jit89/Home-Automation/Hardware/rev_1.0/eagle_schematic.sch

## EAGLE design Hardware/rev_1.0/eagle_schematic.sch (2018-12-20)

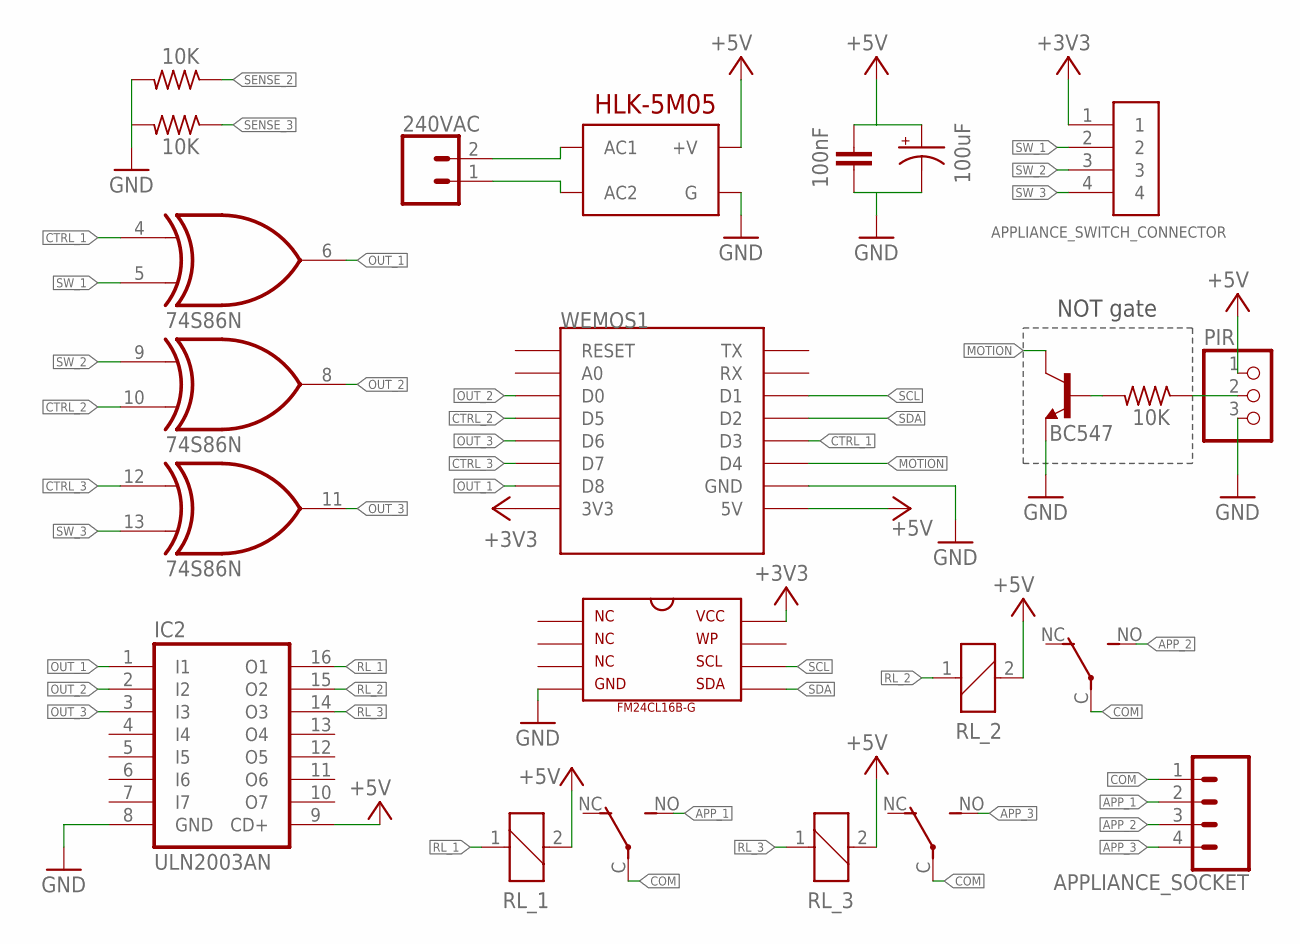
[picture p13: schematic eagle_schematic.sch]

Parts:
240VAC: CONN_025MM; SCREWTERMINAL-5MM-2
APPLIANCE_SOCKET: CONN_04SCREW_LOCK; SCREWTERMINAL-3.5MM-4_LOCK
APPLIANCE_SWITCH_CONNECTOR: 1X4-BIG; 1X04-BIG
C1: 100nF; C5B2.5
C2: 100uF; B45181B
IC1: 74S86N; DIL14
IC2: ULN2003AN; DIL16
PIR: PINHD-1X3CB; 1X03-CLEANBIG
R1, R2, R3: 10K; 0204/7
RL_1, RL_2, RL_3: CQ1-12V; CQ1
T1: BC547; TO92
U$1: HLK-5M05
U$3: FM24CL16B-G
WEMOS1: WEMOS-D1-MINI

Connections:
+3V3: APPLIANCE_SWITCH_CONNECTOR.1, U$3.8, WEMOS1.3V3
+5V: C1.1, C2.+, IC2.9 (CD+), PIR.1, RL_1.2, RL_2.2, RL_3.2, U$1.+V, WEMOS1.5V
APP_1: APPLIANCE_SOCKET.2, RL_1.NO (S)
APP_2: APPLIANCE_SOCKET.3, RL_2.NO (S)
APP_3: APPLIANCE_SOCKET.4, RL_3.NO (S)
COM: APPLIANCE_SOCKET.1, RL_1.C, RL_2.C, RL_3.C
CTRL_1: IC1.4 (I0), WEMOS1.D3
CTRL_2: IC1.10 (I1), WEMOS1.D5
CTRL_3: IC1.12 (I0), WEMOS1.D7
GND: C1.2, C2.-, IC2.8 (GND), PIR.3, R2.2, R3.2, T1.1 (E), U$1.G, U$3.4, WEMOS1.GND
MOTION: T1.3 (C), WEMOS1.D4
unnamed: R1.2, T1.2 (B)
unnamed: PIR.2, R1.1
unnamed: 240VAC.2, U$1.AC1
unnamed: 240VAC.1, U$1.AC2
OUT_1: IC1.6 (O), IC2.1 (I1), WEMOS1.D8
OUT_2: IC1.8 (O), IC2.2 (I2), WEMOS1.D0
OUT_3: IC1.11 (O), IC2.3 (I3), WEMOS1.D6
RL_1: IC2.16 (O1), RL_1.1
RL_2: IC2.15 (O2), RL_2.1
RL_3: IC2.14 (O3), RL_3.1
SCL: U$3.6, WEMOS1.D1
SDA: U$3.5, WEMOS1.D2
SENSE_2: R2.1
SENSE_3: R3.1
SW_1: APPLIANCE_SWITCH_CONNECTOR.2, IC1.5 (I1)
SW_2: APPLIANCE_SWITCH_CONNECTOR.3, IC1.9 (I0)
SW_3: APPLIANCE_SWITCH_CONNECTOR.4, IC1.13 (I1)

Notes on the sheet:
NOT gate
