jit89/Home-Automation/Smartphone_Application/app/src/main/java/com/example/rak3sh/smarthome_app/MainActivity.java

package com.example.rak3sh.smarthome_app;

import android.content.Context;
import android.content.Intent;
import android.net.ConnectivityManager;
import android.net.NetworkInfo;
import android.os.AsyncTask;
import android.os.Bundle;
import android.support.v7.app.AppCompatActivity;
import android.util.Log;
import android.view.View;
import android.widget.ImageButton;
import android.widget.SeekBar;
import android.widget.Spinner;
import android.widget.TextView;
import android.widget.Toast;

import org.json.JSONObject;

import java.io.BufferedReader;
import java.io.BufferedWriter;
import java.io.InputStreamReader;
import java.io.OutputStream;
import java.io.OutputStreamWriter;
import java.net.HttpURLConnection;
import java.net.URL;
import java.net.URLEncoder;
import java.util.Iterator;

import javax.net.ssl.HttpsURLConnection;

public class MainActivity extends AppCompatActivity {


    public String ur = "http://ptsv2.com/t/vbvn/post"; //<<<<<<---url here

    //// TODO: 4/16/2018 onstart status changes


    boolean imButtonStat11 = false;         //ButtonState for on off checking
    boolean imButtonStat21=false;
    boolean imButtonStat31= false;
    boolean imButtonStat41=false;
    boolean imButtonStat12 = false;         //ButtonState for on off checking
    boolean imButtonStat22=false;
    boolean imButtonStat32= false;
    boolean imButtonStat42=false;
    boolean imButtonStat13 = false;         //ButtonState for on off checking
    boolean imButtonStat23=false;
    boolean imButtonStat33= false;
    boolean imButtonStat43=false;
    

    boolean app11, app21, app31, app41,app12,app22,app32,app42,app13,app23,app33 = false,app43;         //bools for json
    int seeka1= 0;
    int seeka2=0;
    int seeka3=0;
    int seekb1=0;
    int seekb2=0;
    int seekb3=0;
    int room=1;


    ImageButton imageButton1,imageButton2,imageButton3,imageButton4,infoButton,roomim1,roomim2,roomim3;

    TextView connectionCheckText;
    TextView appText1,appText2,appText3,appText4;
    SeekBar seekbar1,seekbar2;
     private Spinner spinner2;


    @Override
    protected void onCreate(Bundle savedInstanceState) {

        super.onCreate(savedInstanceState);
        setContentView(R.layout.activity_main);

        imageButton1 = (ImageButton) findViewById(R.id.imButton1);
        imageButton2 = (ImageButton) findViewById(R.id.imButton2);
        imageButton3 = (ImageButton) findViewById(R.id.imButton3);
        imageButton4 = (ImageButton) findViewById(R.id.imButton4);
        infoButton = (ImageButton) findViewById(R.id.infoButton);
        roomim1 = (ImageButton) findViewById(R.id.imroomButton1);
        roomim2 = (ImageButton) findViewById(R.id.imroomButton2);
        roomim3 = (ImageButton) findViewById(R.id.imroomButton3);

        appText1 = (TextView) findViewById(R.id.appText1);
        appText2 = (TextView) findViewById(R.id.appText2);
        appText3 = (TextView) findViewById(R.id.appText3);
        appText4 = (TextView) findViewById(R.id.appText4);

        //connectionCheckText = (TextView) findViewById(R.id.connectionCheckText);

        seekbar1 = (SeekBar) findViewById(R.id.seekBar1);
        seekbar2 = (SeekBar) findViewById(R.id.seekBar2);

        //spinner2=(Spinner)findViewById(R.id.spinner2);


        roomim1.performClick();

        //============================>>>>>>>>>>>info<<<<<<<<<<<<<<<==============================
        infoButton.setOnClickListener(new View.OnClickListener() {
            @Override
            public void onClick(View v) {
                Intent info = new Intent(MainActivity.this, NewActivity.class);
                startActivity(info);
            }
        });


//==============================>>>>>>>>>>>app1<<<<<<<<<<<<<<<<<<===============================
        imageButton1.setOnClickListener(new View.OnClickListener() {
            @Override
            public void onClick(View v) {
                if(room==1) {

                    if (imButtonStat11 == false) {
                        imButtonStat11 = true;
                        // Toast.makeText(getApplicationContext(),"FAN ON",Toast.LENGTH_LONG).show();
                        seekbar1.setProgress(50);
                        seeka1 = 50;
                        appText1.setText("FAN ON (50%)");
                        app11 = true;
                    } else {
                        imButtonStat11 = false;
                        //Toast.makeText(getApplicationContext(),"FAN OFF",Toast.LENGTH_LONG).show();
                        appText1.setText("FAN OFF");
                        seekbar1.setProgress(0);
                        seeka1 = 0;
                        app11 = false;
                    }
                    checkConnection();                //checking connection
                    new postReq().execute();
                }
                else if(room==2){

                    if (imButtonStat12 == false) {
                        imButtonStat12 = true;
                        // Toast.makeText(getApplicationContext(),"FAN ON",Toast.LENGTH_LONG).show();
                        seekbar1.setProgress(50);
                        seeka2 = 50;
                        appText1.setText("FAN ON (50%)");
                        app12 = true;
                    } else {
                        imButtonStat12 = false;
                        //Toast.makeText(getApplicationContext(),"FAN OFF",Toast.LENGTH_LONG).show();
                        appText1.setText("FAN OFF");
                        seekbar1.setProgress(0);
                        seeka2 = 0;
                        app12 = false;
                    }
                    checkConnection();                //checking connection
                    new postReq().execute();
                }
                else if(room==3){
                    if (imButtonStat13 == false) {
                        imButtonStat13 = true;
                        // Toast.makeText(getApplicationContext(),"FAN ON",Toast.LENGTH_LONG).show();
                        seekbar1.setProgress(50);
                        seeka3 = 50;
                        appText1.setText("FAN ON (50%)");
                        app13 = true;
                    } else {
                        imButtonStat13 = false;
                        //Toast.makeText(getApplicationContext(),"FAN OFF",Toast.LENGTH_LONG).show();
                        appText1.setText("FAN OFF");
                        seekbar1.setProgress(0);
                        seeka3 = 0;
                        app13 = false;
                    }
                    checkConnection();                //checking connection
                    new postReq().execute();
                }
                else{
                    Toast.makeText(getApplicationContext(),"Unexpected Error Occured",Toast.LENGTH_LONG).show();

                }//// TODO: 4/15/2018  add thread
            }
        });


        seekbar1.setOnSeekBarChangeListener(new SeekBar.OnSeekBarChangeListener() {


            @Override
            public void onProgressChanged(SeekBar seekBar, int progress, boolean fromUser) {
                if(room==1){seeka1 = progress;}
                else if(room==2){seeka2=progress;}
                else if (room==3){seeka3=progress;}
                else{Toast.makeText(getApplicationContext(),"Unexpected Error Occured",Toast.LENGTH_LONG).show();}

            }

            @Override
            public void onStartTrackingTouch(SeekBar seekBar) {

            }

            @Override
            public void onStopTrackingTouch(SeekBar seekBar) {
                                               //// TODO: 4/15/2018  add thread
                // Toast.makeText(getApplicationContext(),"speed is:"+seek+"%",Toast.LENGTH_SHORT).show();
                if(room==1){ if (seeka1 != 0) {
                    app11 = true;
                    imButtonStat11 = true;
                }
                    appText1.setText("FAN ON" + "(" + seeka1 + "%)");
                }
                else if(room==2){
                    if (seeka2 != 0) {
                        app12 = true;
                        imButtonStat12 = true;
                    }
                    appText1.setText("FAN ON" + "(" + seeka2 + "%)");
                }
                else if(room==3){
                    if (seeka3 != 0) {
                        app13 = true;
                        imButtonStat13 = true;
                    }
                    appText1.setText("FAN ON" + "(" + seeka3 + "%)");
                }

                checkConnection();
                new postReq().execute();



            }
        });
        //=======================>>>>>>>>>>>>>>>>app2<<<<<<<<<<<<<<<====================================

        imageButton2.setOnClickListener(new View.OnClickListener() {
            @Override
            public void onClick(View v) {
                imageButton2.setOnClickListener(new View.OnClickListener() {
                    @Override
                    public void onClick(View v) {

                        checkConnection();
                        if(room==1){
                            if (imButtonStat21 == false) {
                                imButtonStat21 = true;
                                appText2.setText("Light ON");
                                app21 = true;
                            } else {
                                imButtonStat21 = false;
                                appText2.setText("Light OFF");
                                app21 = false;

                            }
                            new postReq().execute();
                        }
                        else if(room==2){ if (imButtonStat22 == false) {
                            imButtonStat22 = true;
                            appText2.setText("Light ON");
                            app22 = true;
                        } else {
                            imButtonStat22 = false;
                            appText2.setText("Light OFF");
                            app22 = false;

                        }
                            new postReq().execute();}
                        else if(room==3){ if (imButtonStat23 == false) {
                            imButtonStat23 = true;
                            appText2.setText("Light ON");
                            app23 = true;
                        } else {
                            imButtonStat23 = false;
                            appText2.setText("Light OFF");
                            app23 = false;

                        }
                            new postReq().execute();}


                    }
                });
            }
        });

//========================>>>>>>>>>>>>>>>>>>>>>app3<<<<<<<<<<<<<<<<<===============================
        imageButton3.setOnClickListener(new View.OnClickListener() {
            @Override
            public void onClick(View v) {
                checkConnection();
                if(room==1){
                    if (imButtonStat31 == false) {
                        imButtonStat31 = true;
                        appText3.setText("Light On");
                        app31 = true;
                    } else {
                        imButtonStat31 = false;
                        app31 = false;
                        appText3.setText("Light OFF");
                    }
                    new postReq().execute();
                }
                else if(room==2){

                    if (imButtonStat32 == false) {
                        imButtonStat32 = true;
                        appText3.setText("Light On");
                        app32 = true;
                    } else {
                        imButtonStat32 = false;
                        app32 = false;
                        appText3.setText("Light OFF");
                    }
                    new postReq().execute();
                }
                else if(room==3){ if (imButtonStat33 == false) {
                    imButtonStat33 = true;
                    appText3.setText("Light On");
                    app33 = true;
                } else {
                    imButtonStat33 = false;
                    app33 = false;
                    appText3.setText("Light OFF");
                }
                    new postReq().execute();}




                //todo light2 logic
            }
        });

//===================>>>>>>>>>>>>>>>>>app4<<<<<<<<<<<<<<<<<<<<<<<<==================================
        imageButton4.setOnClickListener(new View.OnClickListener() {
            @Override
            public void onClick(View v) {
                checkConnection();
                if(room==1){if (imButtonStat41 == false) {
                    imButtonStat41 = true;
                    // Toast.makeText(getApplicationContext(),"FAN ON",Toast.LENGTH_LONG).show();
                    seekbar2.setProgress(50);
                    seekb1 = 50;
                    appText4.setText("FAN ON (50%)");
                    app41 = true;
                } else {
                    imButtonStat41 = false;
                    //Toast.makeText(getApplicationContext(),"FAN OFF",Toast.LENGTH_LONG).show();
                    appText4.setText("FAN OFF");
                    seekbar2.setProgress(0);
                    seekb1 = 0;
                    app41 = false;
                }
                new postReq().execute();}
                else if(room==2){if (imButtonStat42 == false) {
                    imButtonStat42 = true;
                    // Toast.makeText(getApplicationContext(),"FAN ON",Toast.LENGTH_LONG).show();
                    seekbar2.setProgress(50);
                    seekb2 = 50;
                    appText4.setText("FAN ON (50%)");
                    app42 = true;
                } else {
                    imButtonStat42 = false;
                    //Toast.makeText(getApplicationContext(),"FAN OFF",Toast.LENGTH_LONG).show();
                    appText4.setText("FAN OFF");
                    seekbar2.setProgress(0);
                    seekb2 = 0;
                    app42 = false;
                }
                    new postReq().execute();}
                else if(room==3){
                    if (imButtonStat43 == false) {
                        imButtonStat43 = true;
                        // Toast.makeText(getApplicationContext(),"FAN ON",Toast.LENGTH_LONG).show();
                        seekbar2.setProgress(50);
                        seekb3 = 50;
                        appText4.setText("FAN ON (50%)");
                        app43 = true;
                    } else {
                        imButtonStat43 = false;
                        //Toast.makeText(getApplicationContext(),"FAN OFF",Toast.LENGTH_LONG).show();
                        appText4.setText("FAN OFF");
                        seekbar2.setProgress(0);
                        seekb3 = 0;
                        app43 = false;
                    }
                    new postReq().execute();
                }
                else{
                    Toast.makeText(getApplicationContext(),"Unexpected Error Occured",Toast.LENGTH_LONG);

                }

                           //// TODO: 4/15/2018  add thread

            }
        });
        seekbar2.setOnSeekBarChangeListener(new SeekBar.OnSeekBarChangeListener() {
            @Override
            public void onProgressChanged(SeekBar seekBar, int progress, boolean fromUser) {
                if(room==1){seekb1 = progress;}
                else if(room==2){seekb2 = progress;}
                else if(room==3){seekb3 = progress;}

            }

            @Override
            public void onStartTrackingTouch(SeekBar seekBar) {

            }

            @Override
            public void onStopTrackingTouch(SeekBar seekBar) {
                checkConnection();
                if(room==1){if (seekb1 != 0) {
                    checkConnection();
                    app41 = true;
                    imButtonStat41 = true;
                }
                    appText4.setText("FAN ON" + "(" + seekb1 + "%)");}
                else if(room==2){if (seekb2 != 0) {
                    checkConnection();
                    app42 = true;
                    imButtonStat42 = true;
                }
                    appText4.setText("FAN ON" + "(" + seekb2 + "%)");}
                else if(room==3){if (seekb3 != 0) {
                    checkConnection();
                    app43 = true;
                    imButtonStat43 = true;
                }
                    appText4.setText("FAN ON" + "(" + seekb3 + "%)");}

                new postReq().execute();
            }
        });


        //=======================>>>>>>>>>>>>>room1<<<<<<<<<<<<<<<<<<<<<<==================================
        roomim1.setOnClickListener(new View.OnClickListener() {
            @Override
            public void onClick(View v) {
                room=1;
                roomim1.setBackgroundColor(0xFF6daf8f);
                roomim2.setBackgroundColor(0xFF3eb291);
                roomim3.setBackgroundColor(0xFF3eb291);

                if(app11){appText1.setText("FAN ON" + "(" + seeka1 + "%)");
                seekbar1.setProgress(seeka1);}
                else{appText1.setText("FAN OFF");
                seekbar1.setProgress(0);}

                if(app21){appText2.setText("LIGHT ON");}
                else{appText2.setText("LIGHT OFF");}

                if(app31){appText3.setText("LIGHT ON");}
                else{appText3.setText("LIGHT OFF");}

                if(app41){appText4.setText("FAN ON" + "(" + seekb1 + "%)");
                seekbar2.setProgress(seekb1);}
                else{appText4.setText("FAN OFF");
                seekbar2.setProgress(0);}


            }
        });

        roomim2.setOnClickListener(new View.OnClickListener() {
            @Override
            public void onClick(View v) {
                room=2;
                roomim2.setBackgroundColor(0xFF6daf8f);
                roomim1.setBackgroundColor(0xFF3eb291);
                roomim3.setBackgroundColor(0xFF3eb291);

                if(app12){appText1.setText("FAN ON" + "(" + seeka2 + "%)");
                seekbar1.setProgress(seeka2);}
                else{appText1.setText("FAN OFF");
                seekbar1.setProgress(0);}

                if(app22){appText2.setText("LIGHT ON");}
                else{appText2.setText("LIGHT OFF");}

                if(app32){appText3.setText("LIGHT ON");}
                else{appText3.setText("LIGHT OFF");}

                if(app42){appText4.setText("FAN ON" + "(" + seekb2 + "%)");
                seekbar2.setProgress(seekb2);}
                else{appText4.setText("FAN OFF");
                seekbar2.setProgress(0);}


            }
        });
        roomim3.setOnClickListener(new View.OnClickListener() {
            @Override
            public void onClick(View v) {
                room=3;
                roomim3.setBackgroundColor(0xFF6daf8f);
                roomim1.setBackgroundColor(0xFF3eb291);
                roomim2.setBackgroundColor(0xFF3eb291);

                if(app13){appText1.setText("FAN ON" + "(" + seeka3 + "%)");
                seekbar1.setProgress(seeka3);}
                else{appText1.setText("FAN OFF");
                seekbar1.setProgress(0);}

                if(app23){appText2.setText("LIGHT ON");}
                else{appText2.setText("LIGHT OFF");}

                if(app33){appText3.setText("LIGHT ON");}
                else{appText3.setText("LIGHT OFF");}

                if(app43){appText4.setText("FAN ON" + "(" + seekb3 + "%)");
                seekbar2.setProgress(seekb3);}
                else{appText4.setText("FAN OFF");
                seekbar1.setProgress(0);}
            }
        });
        roomim1.performClick();


    }
    //---------------------------------connectivity checking------------------

    /*public Boolean connectionCheck() {                                       //// TODO: 4/15/2018 connectivity in thread
        try {
            Process p1 = java.lang.Runtime.getRuntime().exec("ping -c 1 www.google.com");
            int returnVal = p1.waitFor();
            boolean reachable = (returnVal == 0);
            return reachable;
        } catch (Exception e) {
            // TODO Auto-generated catch block
            e.printStackTrace();
        }
        return false;
    }
*/
    protected boolean isOnline() {
        ConnectivityManager cm = (ConnectivityManager) getSystemService(Context.CONNECTIVITY_SERVICE);
        NetworkInfo netInfo = cm.getActiveNetworkInfo();
        if (netInfo != null && netInfo.isConnectedOrConnecting()) {
            return true;
        } else {
            return false;
        }
    }


    public void checkConnection() {
        connectionCheckText = (TextView) findViewById(R.id.connectionCheckText);

        if (isOnline()) {
            Log.d("Connection Status:", "ok");
            connectionCheckText.setText("  ");

        } else {
            connectionCheckText.setText("NO INTERNET CONNECTION!!");
            Log.d("connection Status:", "no connection");
            Toast.makeText(MainActivity.this, "Please Check the connection,or\n \t\t\t" +
                    "Try agatn in a while ", Toast.LENGTH_LONG).show();

        }
    }


    //-------------------------------------HTTP posting-----------------------

    public class postReq extends AsyncTask<String, Void, String> {

        protected void onPreExecute(String result) {


        }

        @Override
        protected String doInBackground(String... params) {


            try {

                URL url = new URL(ur);

                JSONObject postDataParams = new JSONObject();
                if(room==1){
                postDataParams.put("room1",1);
                postDataParams.put("app1", app11);
                postDataParams.put("app1a", seeka1 * (10.24));
                postDataParams.put("app2", app21);
                postDataParams.put("app3", app31);
                postDataParams.put("app4", app41);
                postDataParams.put("app4a",seekb1*10.24);
                }
                else if(room==2){

                    postDataParams.put("room1",2);
                    postDataParams.put("app1", app12);
                    postDataParams.put("app1a", seeka2 * (10.24));
                    postDataParams.put("app2", app22);
                    postDataParams.put("app3", app32);
                    postDataParams.put("app4", app42);
                    postDataParams.put("app4a",seekb2*10.24);
                }
                else if(room==3){

                    postDataParams.put("room1",3);
                    postDataParams.put("app1", app13);
                    postDataParams.put("app1a", seeka3 * (10.24));
                    postDataParams.put("app2", app23);
                    postDataParams.put("app3", app33);
                    postDataParams.put("app4", app43);
                    postDataParams.put("app4a",seekb3*10.24);
                }

                Log.e("params", postDataParams.toString());


                HttpURLConnection conn = (HttpURLConnection) url.openConnection();
                conn.setReadTimeout(15000 /* milliseconds */);
                conn.setConnectTimeout(15000 /* milliseconds */);
                conn.setRequestMethod("POST");
                conn.setDoInput(true);
                conn.setDoOutput(true);
                OutputStream os = conn.getOutputStream();
                BufferedWriter writer = new BufferedWriter(
                        new OutputStreamWriter(os, "UTF-8"));
                writer.write(getPostDataString(postDataParams));

                writer.flush();
                writer.close();
                os.close();

                int responseCode = conn.getResponseCode();

                if (responseCode == HttpsURLConnection.HTTP_OK) {

                    BufferedReader in = new BufferedReader(
                            new InputStreamReader(
                                    conn.getInputStream()));
                    StringBuffer sb = new StringBuffer("");
                    String line = "";

                    while ((line = in.readLine()) != null) {

                        sb.append(line);
                        break;
                    }

                    in.close();
                    return sb.toString();

                } else {
                    return new String("false : " + responseCode);
                }
            } catch (Exception e) {
                return new String("Exception: " + e.getMessage());
            }


            //return null;
        }


        protected void onPostExecute(String result) {
            // Toast.makeText(getApplicationContext(),result,Toast.LENGTH_LONG).show();
            Log.d("Post Status:", result);
        }
    }

    public String getPostDataString(JSONObject params) throws Exception {

        StringBuilder result = new StringBuilder();
        boolean first = true;

        Iterator<String> itr = params.keys();

        while (itr.hasNext()) {

            String key = itr.next();
            Object value = params.get(key);

            if (first)
                first = false;
            else
                result.append("&");

            result.append(URLEncoder.encode(key, "UTF-8"));
            result.append("=");
            result.append(URLEncoder.encode(value.toString(), "UTF-8"));

        }
        return result.toString();
    }
}
