jit89/Home-Automation/Micropython/boot.py

# This file is executed on every boot (including wake-boot from deepsleep)

import esp

esp.osdebug(None)

import gc

# import webrepl
# webrepl.start()
gc.collect()

import os

os.chdir('Micropython')
import main

main.main()
